zotbins/waste_watcher/guide/underside_view.jpg

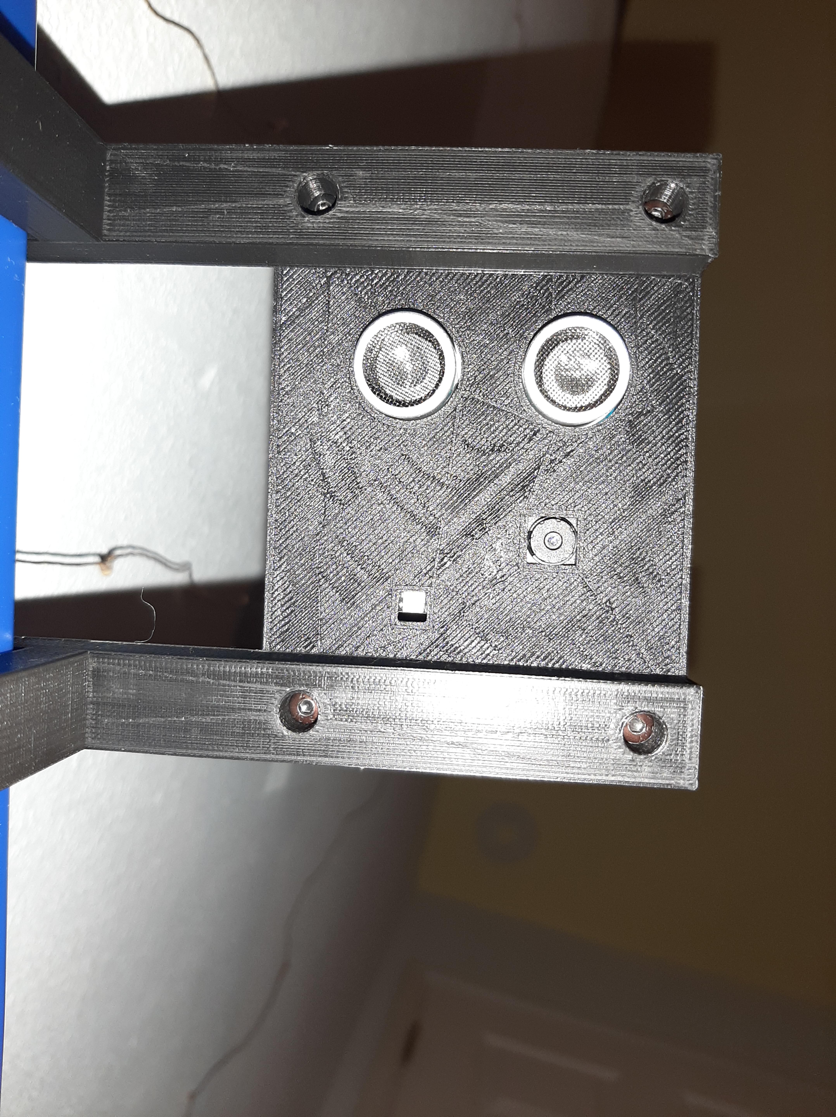
guide/underside_view.jpg
